lrolomeli/exoesqueleto-mano/programacion/pythongui/boton_stop.jpg

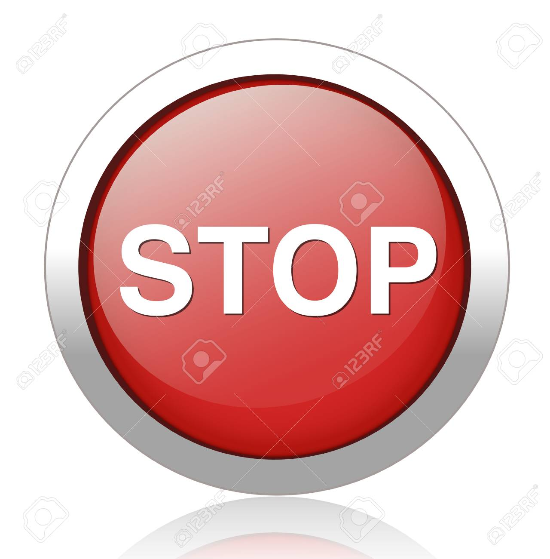
programacion/pythongui/boton_stop.jpg
