lrolomeli/exoesqueleto-mano/programacion/pythongui/boton_start.jpg

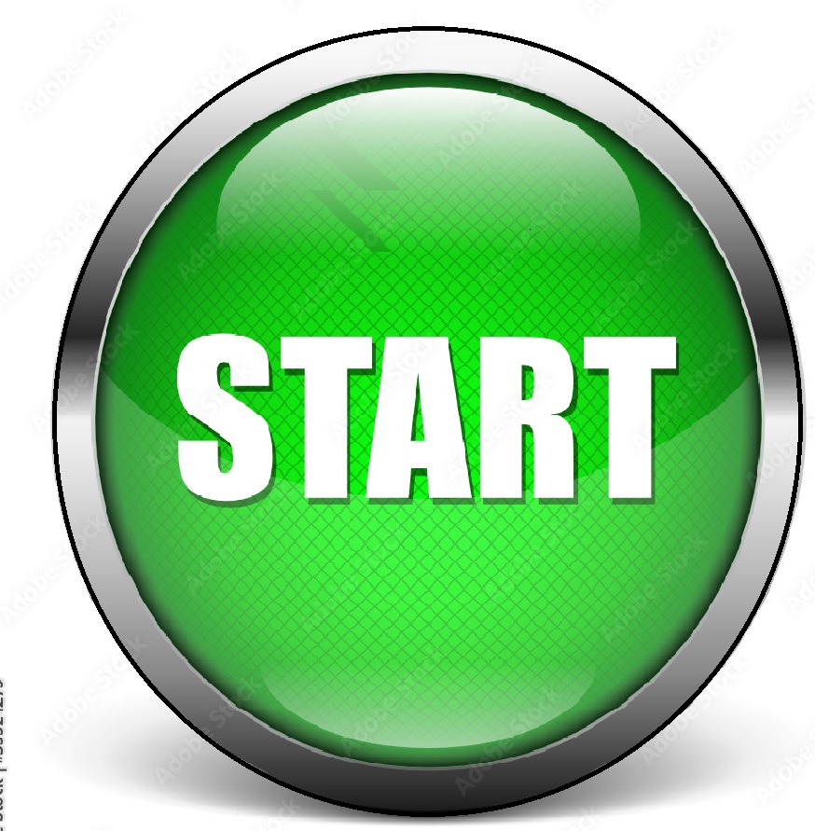
programacion/pythongui/boton_start.jpg
