lrolomeli/exoesqueleto-mano/programacion/pythongui/elegant.png

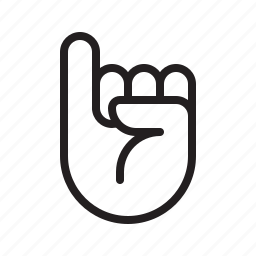
programacion/pythongui/elegant.png
