lrolomeli/exoesqueleto-mano/programacion/pythongui/exoesk.png

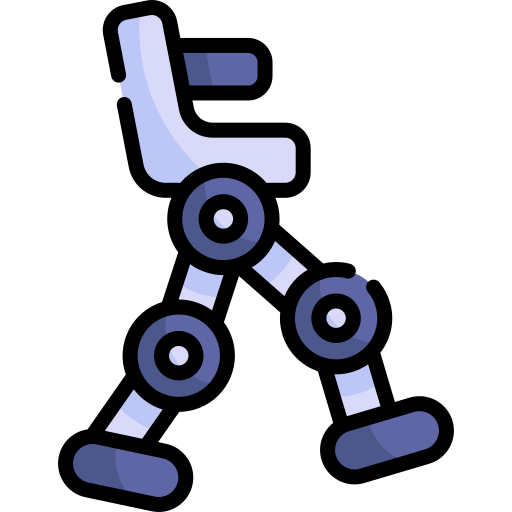
programacion/pythongui/exoesk.png
