lrolomeli/exoesqueleto-mano/programacion/pythongui/fdown.png

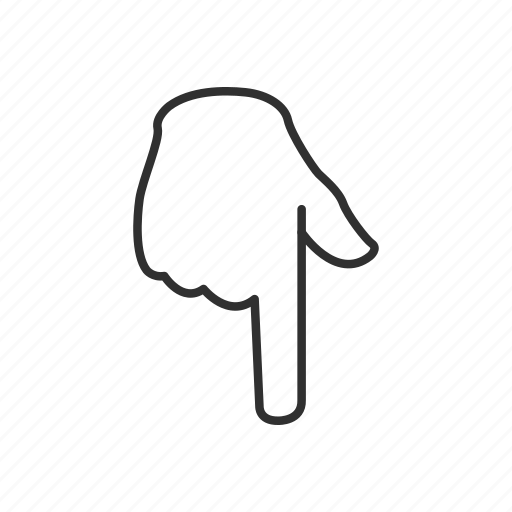
programacion/pythongui/fdown.png
