lrolomeli/exoesqueleto-mano/programacion/pythongui/left_hand.png

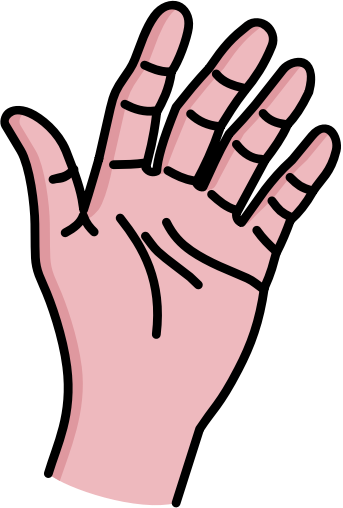
programacion/pythongui/left_hand.png
