lrolomeli/exoesqueleto-mano/programacion/pythongui/rck.png

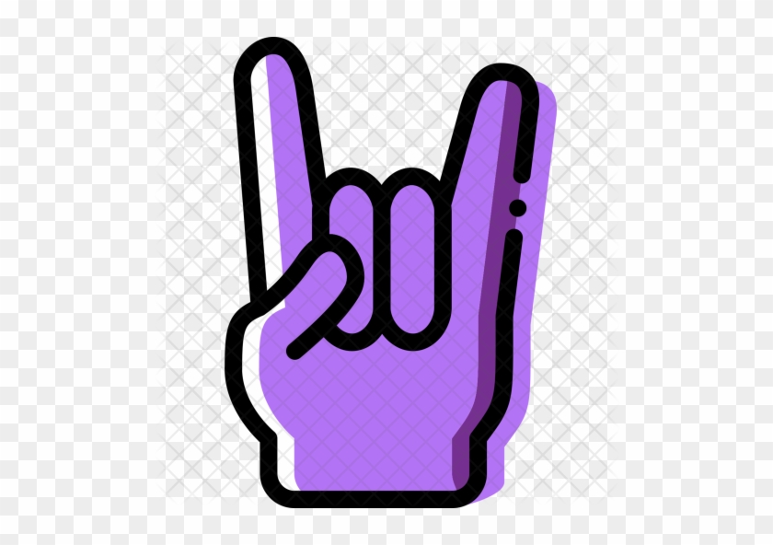
programacion/pythongui/rck.png
