lrolomeli/exoesqueleto-mano/programacion/pythongui/rocki.png

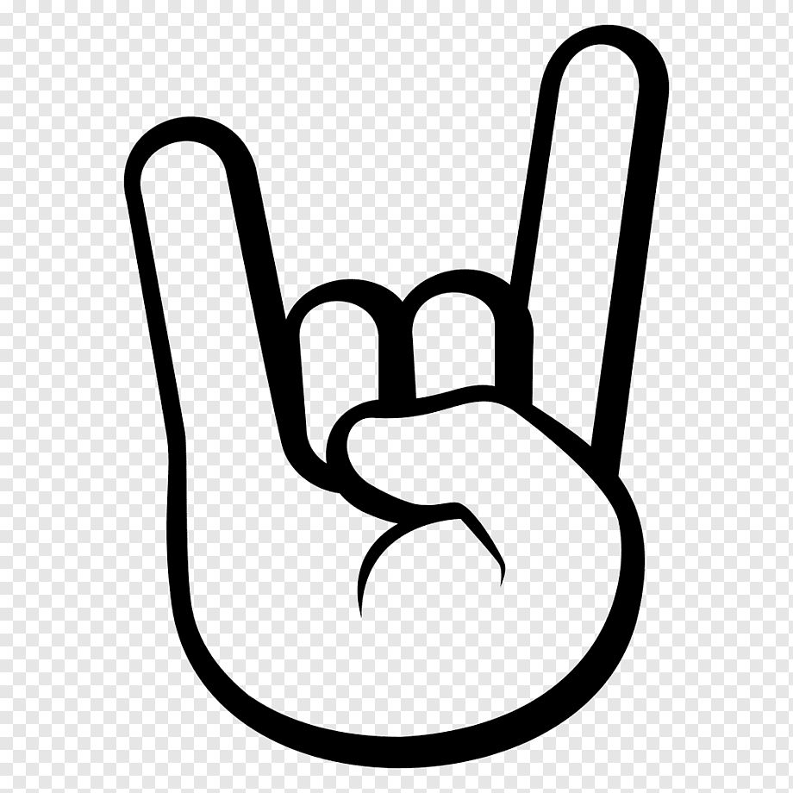
programacion/pythongui/rocki.png
