lrolomeli/exoesqueleto-mano/programacion/pythongui/start-button.jpg

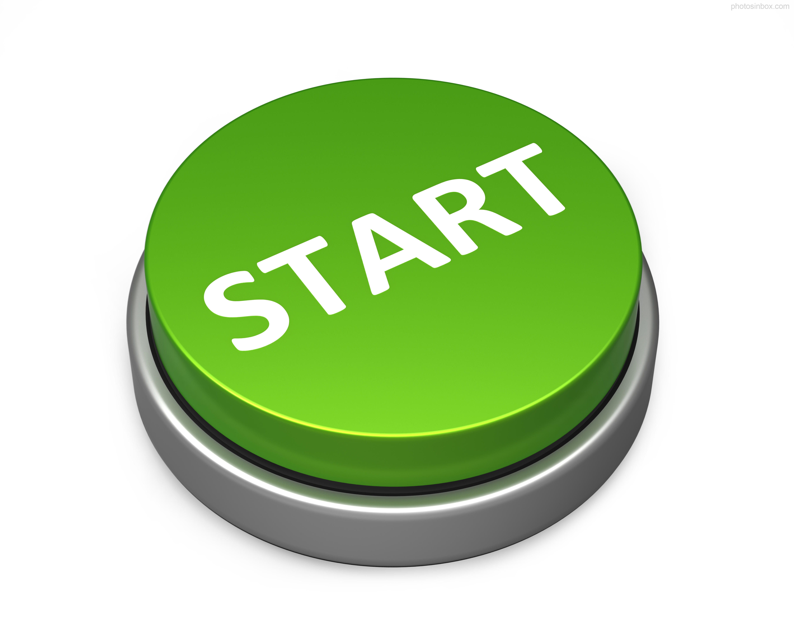
programacion/pythongui/start-button.jpg
