lrolomeli/exoesqueleto-mano/stl_impresion/cubierta1.STL

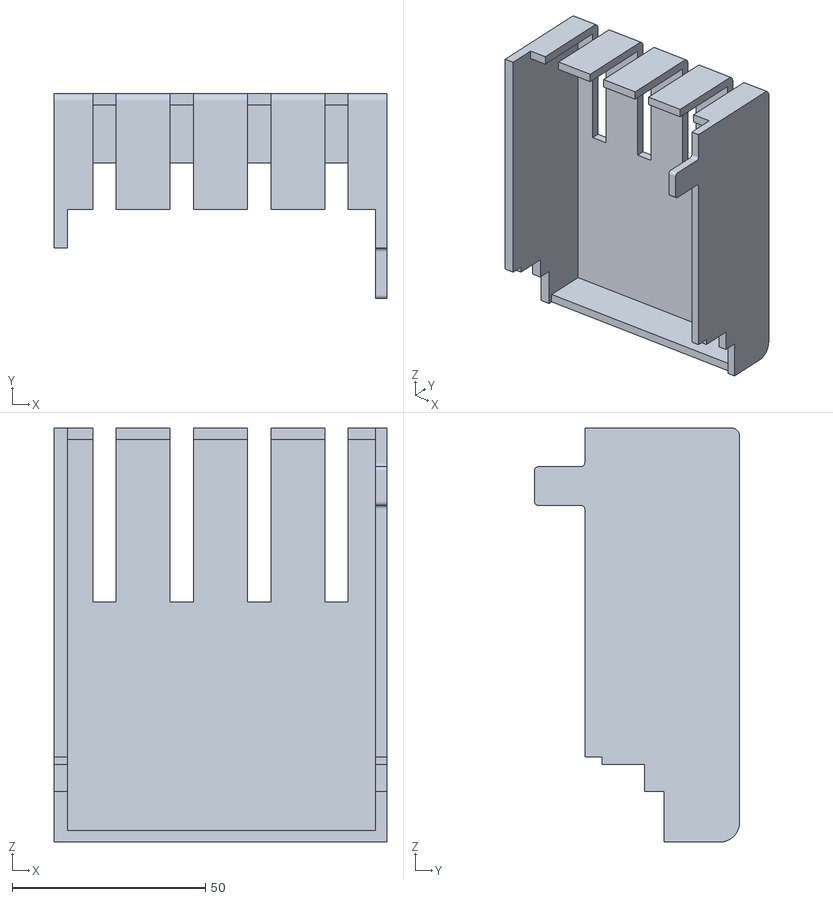
[picture p27: CAD file, 2023-11-08]
stl_impresion/cubierta1.STL
86.0 x 53.0 x 107.0
