lrolomeli/exoesqueleto-mano/mano_p/f3-medio.SLDPRT

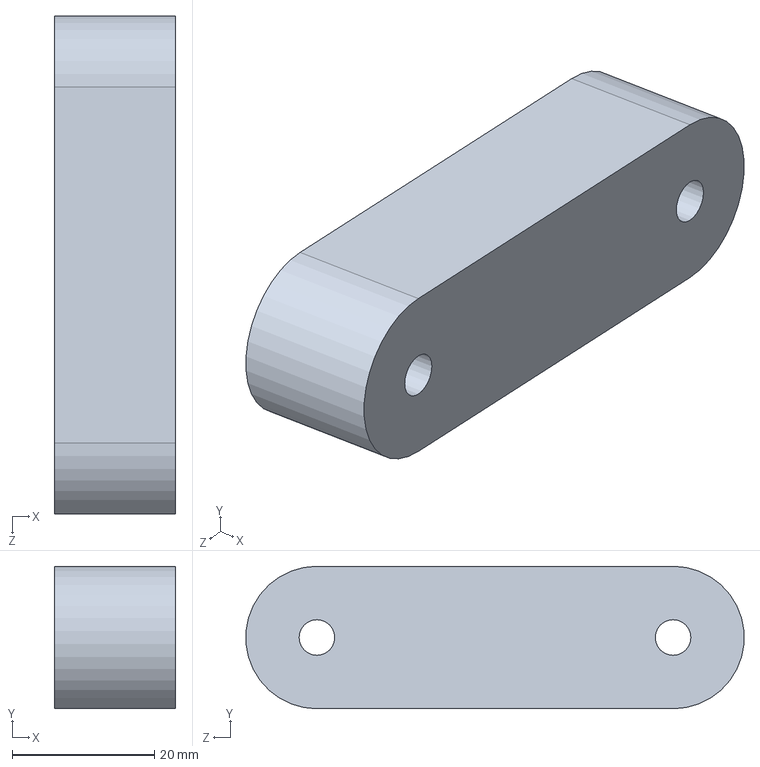
[picture p28: CAD file, 2023-06-01]
mano_p/f3-medio.SLDPRT
17.0 x 20.0 x 69.9 mm
