lrolomeli/exoesqueleto-mano/piezas/cubierta.SLDPRT

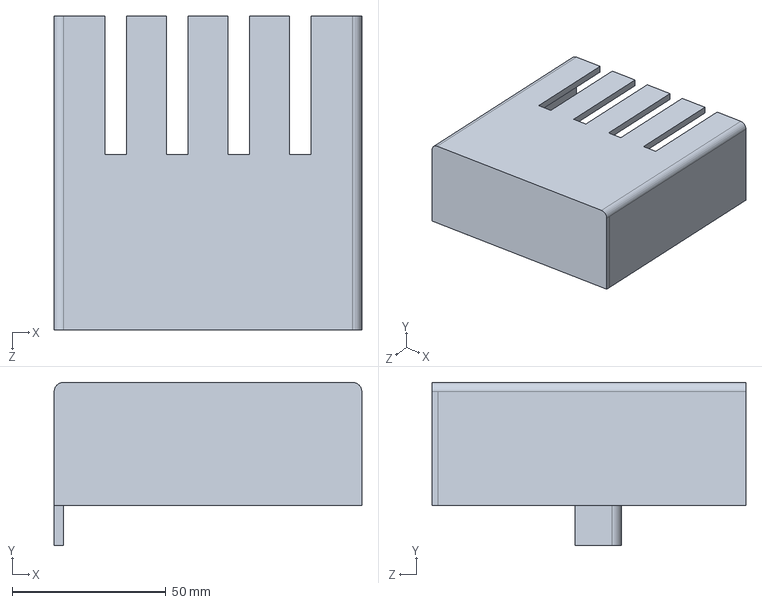
[picture p29: CAD file, 2023-11-08]
piezas/cubierta.SLDPRT
100.0 x 53.0 x 102.0 mm
