lrolomeli/exoesqueleto-mano/stl_impresion/vastago_pm.STL

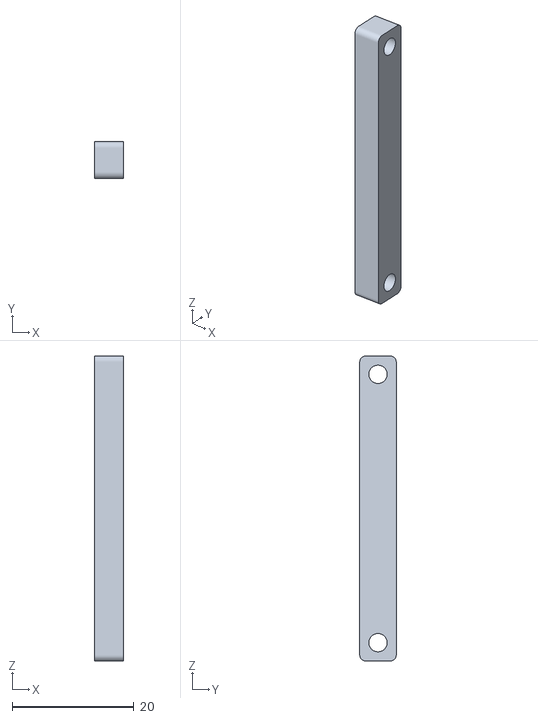
[picture p30: CAD file, 2023-09-11]
stl_impresion/vastago_pm.STL
4.80 x 6.00 x 50.0
