lrolomeli/exoesqueleto-mano/mano_p/f2-medio.SLDPRT

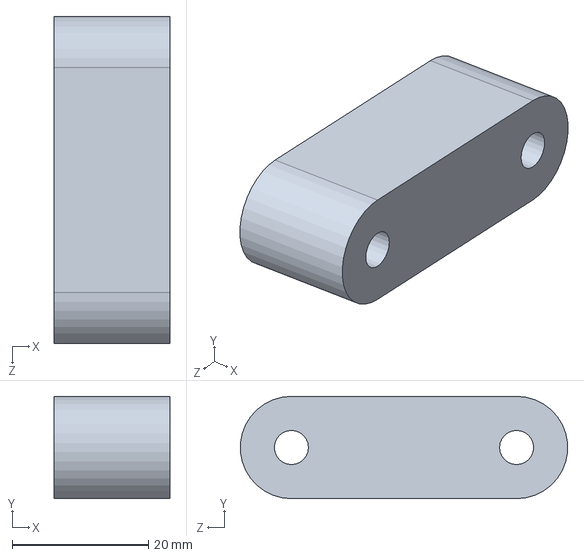
[picture p31: CAD file, 2023-06-01]
mano_p/f2-medio.SLDPRT
17.0 x 15.0 x 47.9 mm
