lrolomeli/exoesqueleto-mano/stl_impresion/tapa_base.STL

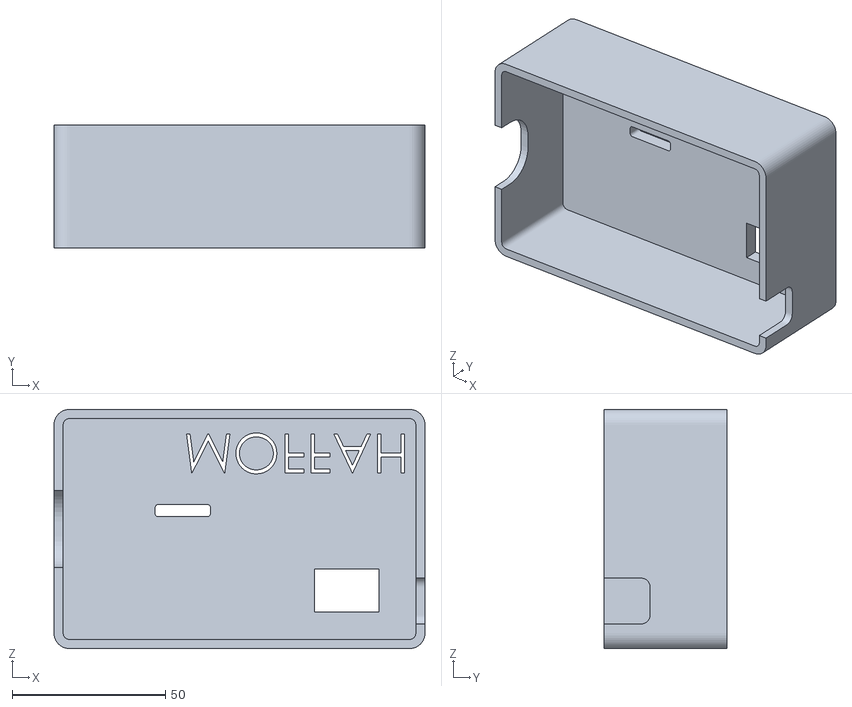
[picture p32: CAD file, 2023-09-11]
stl_impresion/tapa_base.STL
121.0 x 40.0 x 78.0
