lrolomeli/exoesqueleto-mano/mano_p/f1-medio.SLDPRT

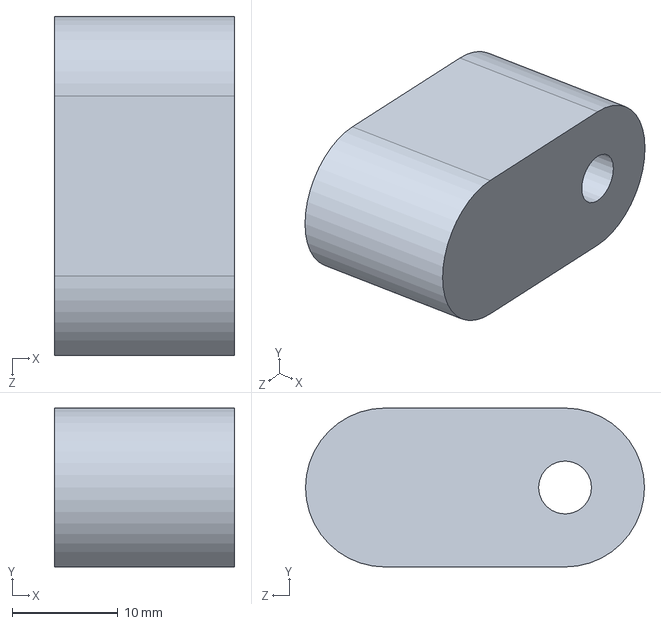
[picture p33: CAD file, 2023-06-01]
mano_p/f1-medio.SLDPRT
17.0 x 15.0 x 32.0 mm
