lrolomeli/exoesqueleto-mano/stl_impresion/base_bateria_pcb.STL

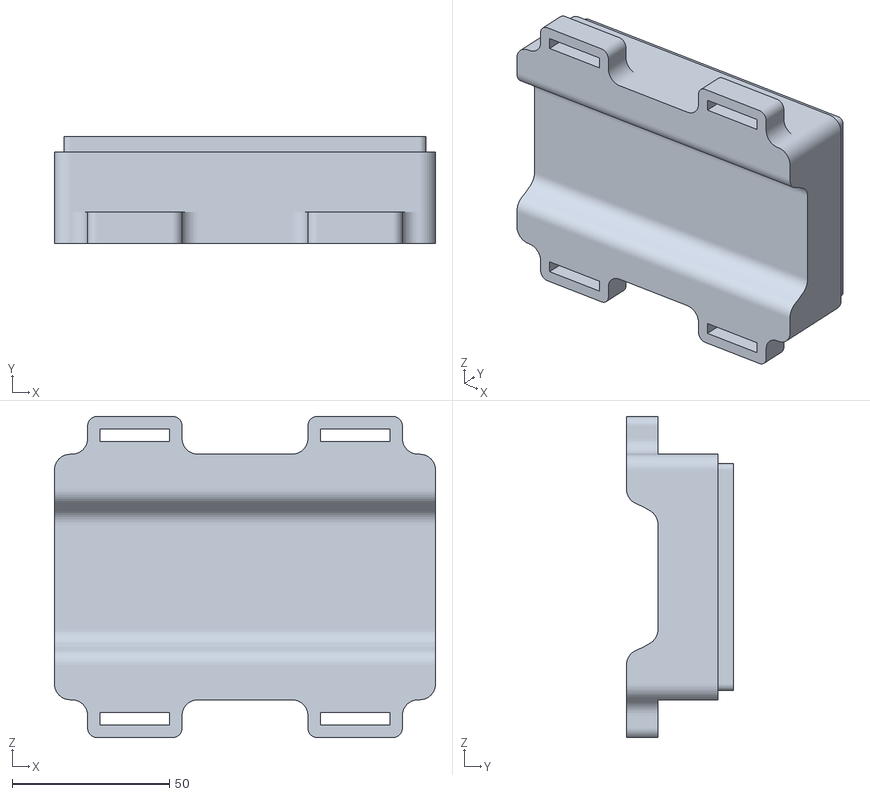
[picture p34: CAD file, 2023-09-11]
stl_impresion/base_bateria_pcb.STL
121.0 x 34.0 x 102.0
