lrolomeli/exoesqueleto-mano/stl_impresion/vastago-y-largo-pulgar.STL

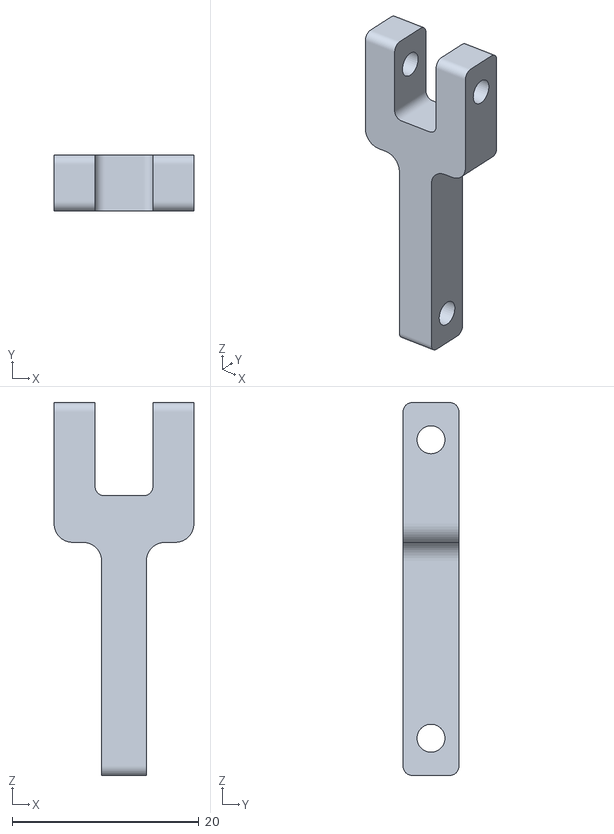
[picture p35: CAD file, 2023-09-11]
stl_impresion/vastago-y-largo-pulgar.STL
15.0 x 6.00 x 40.0
