lrolomeli/exoesqueleto-mano/mano_p/f3-anular.SLDPRT

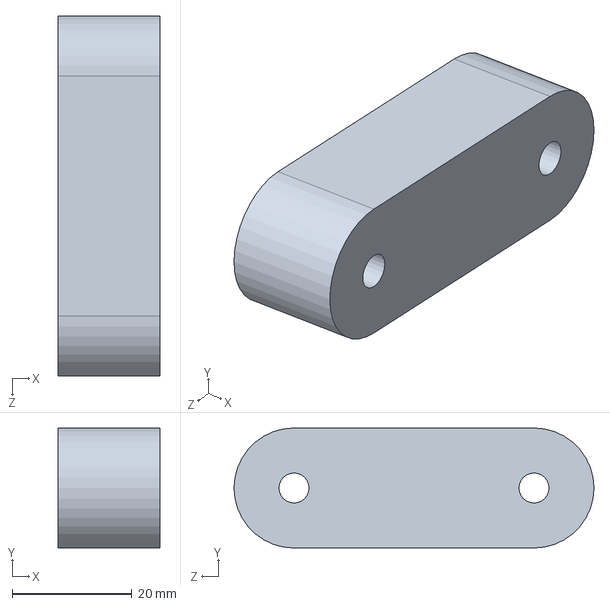
[picture p36: CAD file, 2023-06-01]
mano_p/f3-anular.SLDPRT
17.0 x 20.0 x 60.0 mm
