lrolomeli/exoesqueleto-mano/mano_p/torso-mano.SLDPRT

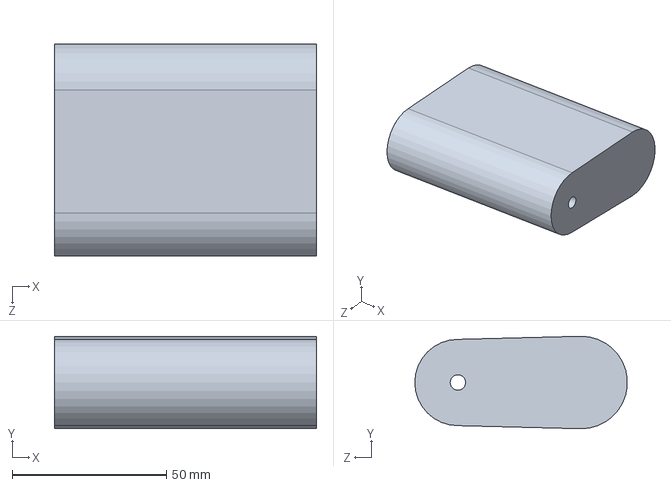
[picture p37: CAD file, 2023-05-29]
mano_p/torso-mano.SLDPRT
85.0 x 30.0 x 68.9 mm
