lrolomeli/exoesqueleto-mano/piezas/vastago-y-largo-indice.SLDPRT

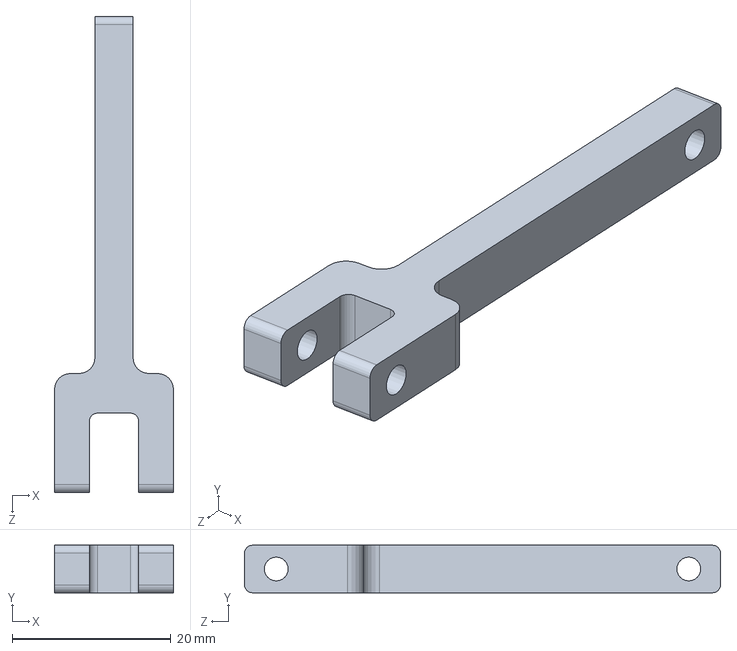
[picture p38: CAD file, 2023-09-11]
piezas/vastago-y-largo-indice.SLDPRT
15.0 x 6.00 x 60.0 mm
