lrolomeli/exoesqueleto-mano/stl_impresion/abrazadera_completa.STL

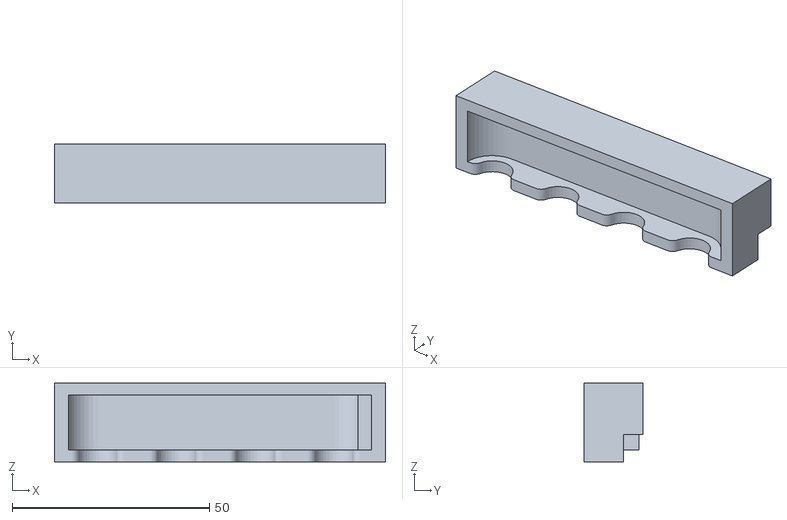
[picture p39: CAD file, 2023-07-09]
stl_impresion/abrazadera_completa.STL
84.0 x 15.0 x 20.0
