lrolomeli/exoesqueleto-mano/stl_impresion/abrazadera_completa_2pza.STL

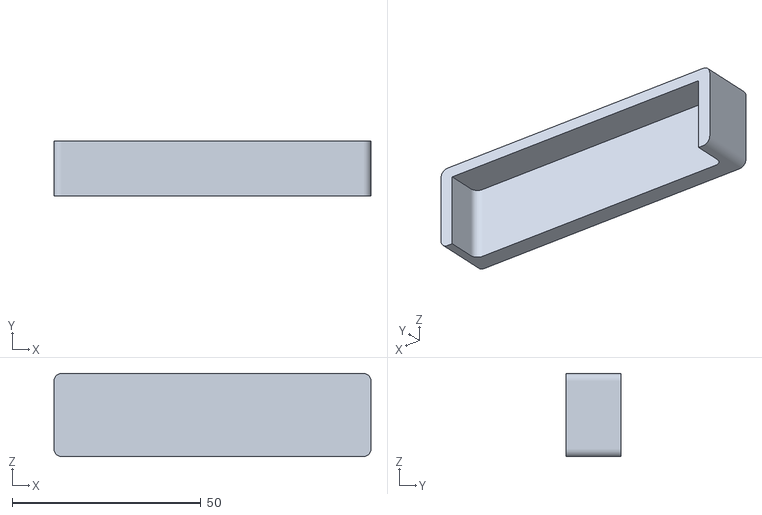
[picture p40: CAD file, 2023-07-09]
stl_impresion/abrazadera_completa_2pza.STL
84.0 x 14.5 x 22.0
