lrolomeli/exoesqueleto-mano/piezas/cincho_belcro.SLDPRT

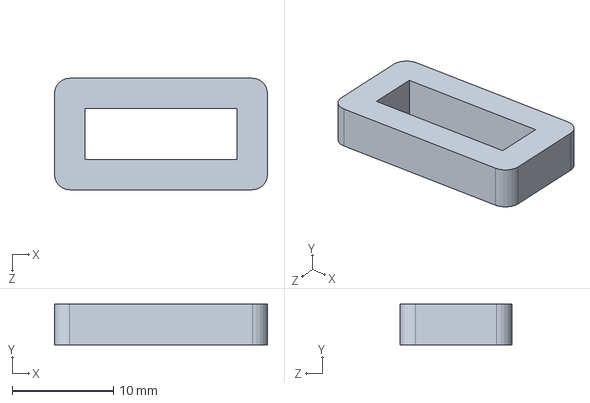
[picture p41: CAD file, 2023-07-09]
piezas/cincho_belcro.SLDPRT
21.0 x 4.00 x 11.0 mm
