lrolomeli/exoesqueleto-mano/stl_impresion/palanca-medio.STL

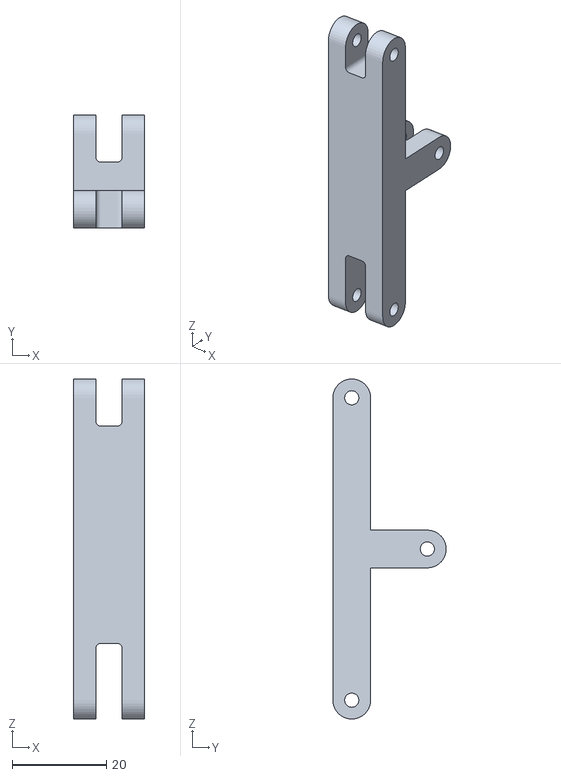
[picture p42: CAD file, 2023-07-03]
stl_impresion/palanca-medio.STL
15.0 x 24.0 x 72.0
