lrolomeli/exoesqueleto-mano/mano_p/f2-anular.SLDPRT

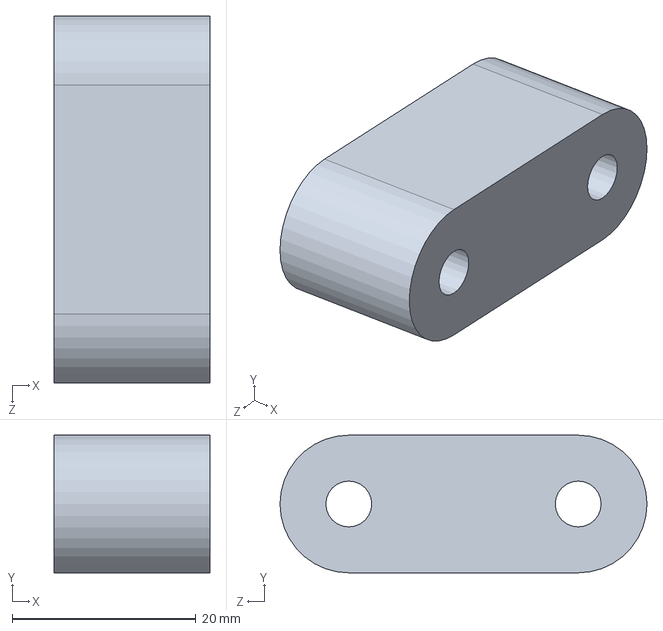
[picture p43: CAD file, 2023-05-08]
mano_p/f2-anular.SLDPRT
17.0 x 15.0 x 40.0 mm
