lrolomeli/exoesqueleto-mano/stl_impresion/base-principal-p2.STL

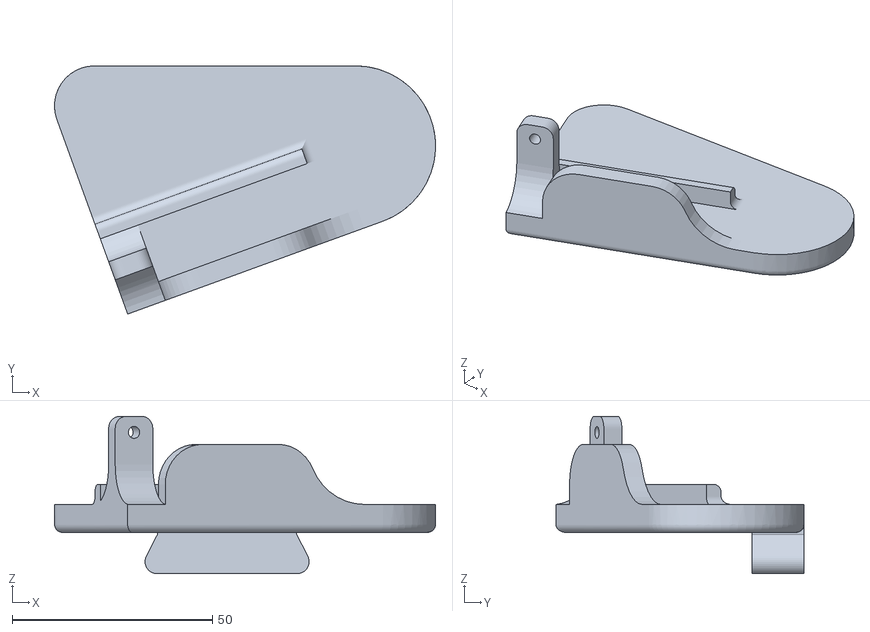
[picture p44: CAD file, 2023-07-03]
stl_impresion/base-principal-p2.STL
95.2 x 62.0 x 39.3
