lrolomeli/exoesqueleto-mano/mano_p/falange4_p.SLDPRT

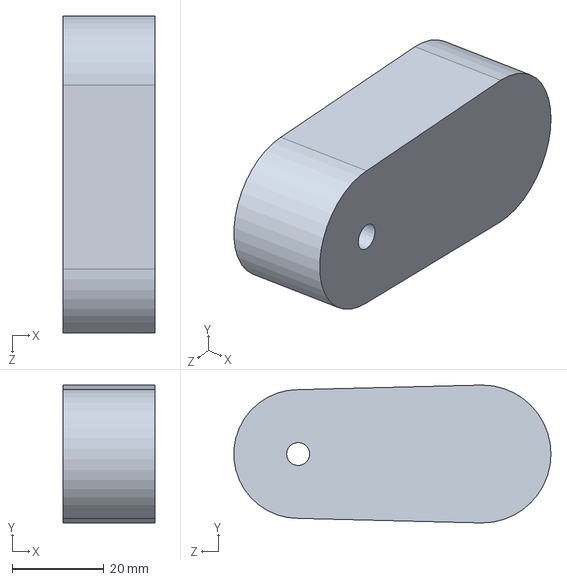
[picture p45: CAD file, 2023-05-08]
mano_p/falange4_p.SLDPRT
20.0 x 30.0 x 69.0 mm
