lrolomeli/exoesqueleto-mano/stl_impresion/base-principal-completa.STL

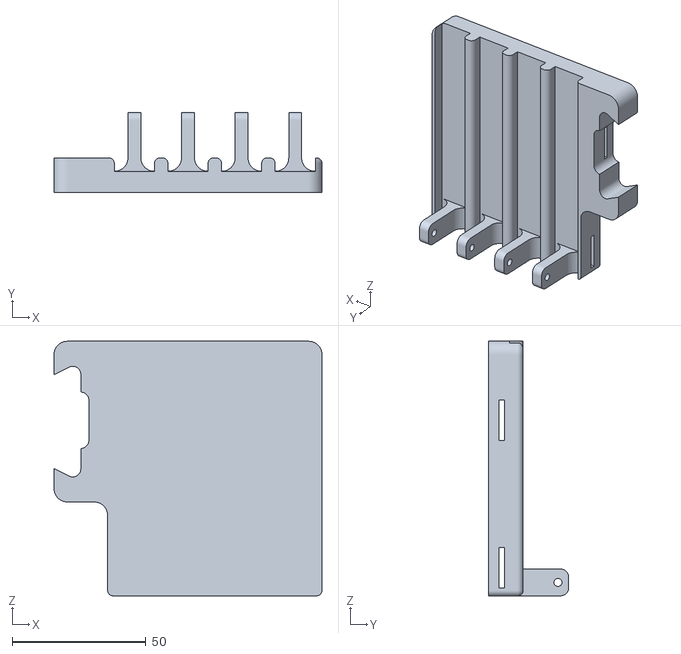
[picture p46: CAD file, 2023-07-03]
stl_impresion/base-principal-completa.STL
100.0 x 30.0 x 95.0
