lrolomeli/exoesqueleto-mano/piezas/abrazadera.SLDPRT

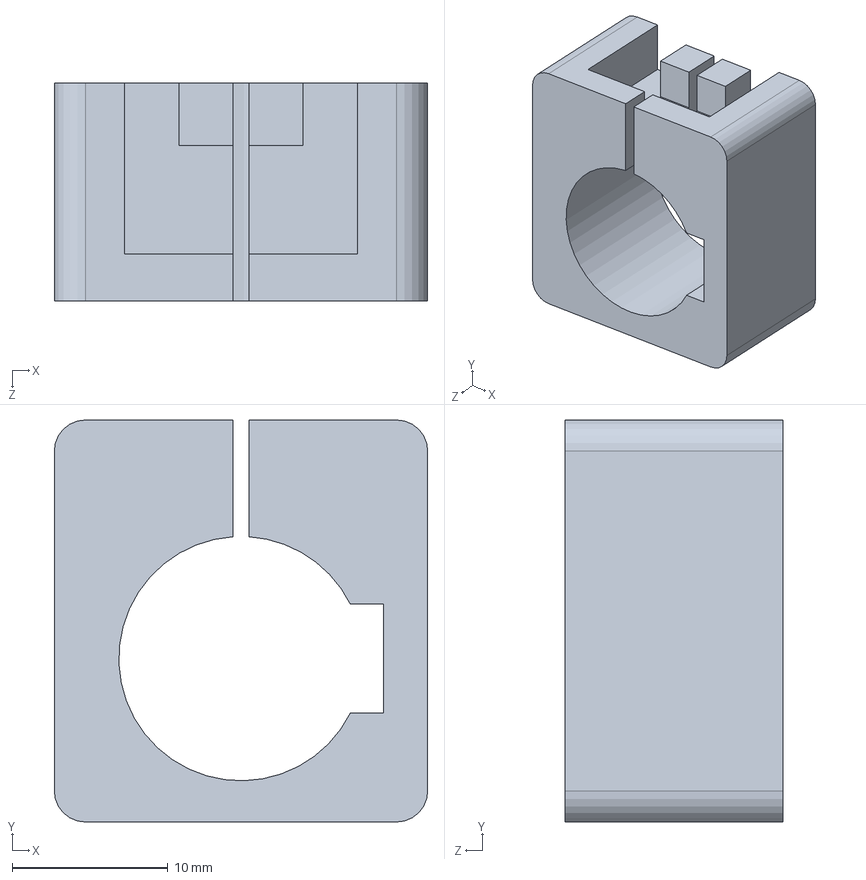
[picture p47: CAD file, 2023-07-03]
piezas/abrazadera.SLDPRT
24.0 x 25.8 x 14.0 mm
