lrolomeli/exoesqueleto-mano/piezas/guia-lineal.SLDPRT

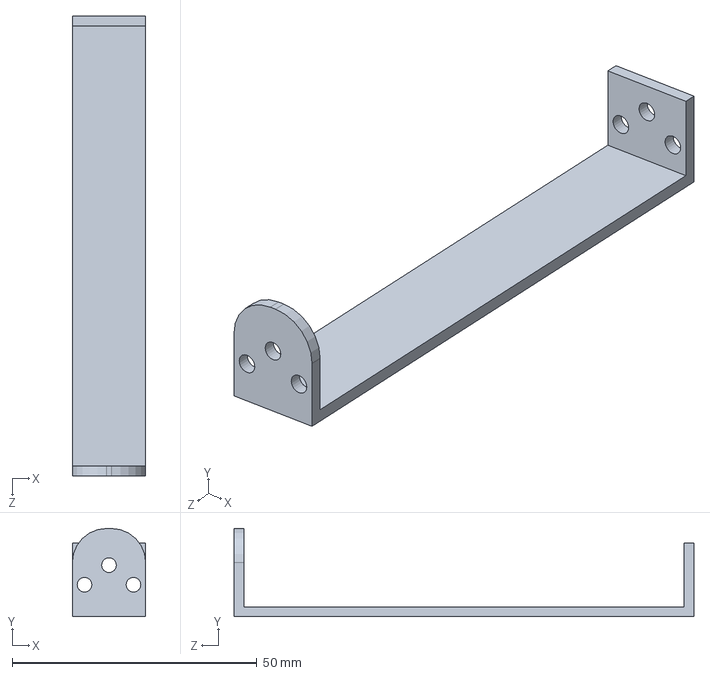
[picture p48: CAD file, 2023-07-03]
piezas/guia-lineal.SLDPRT
15.0 x 18.0 x 94.0 mm
