lrolomeli/exoesqueleto-mano/stl_impresion/vastago-y-largo-menique.STL

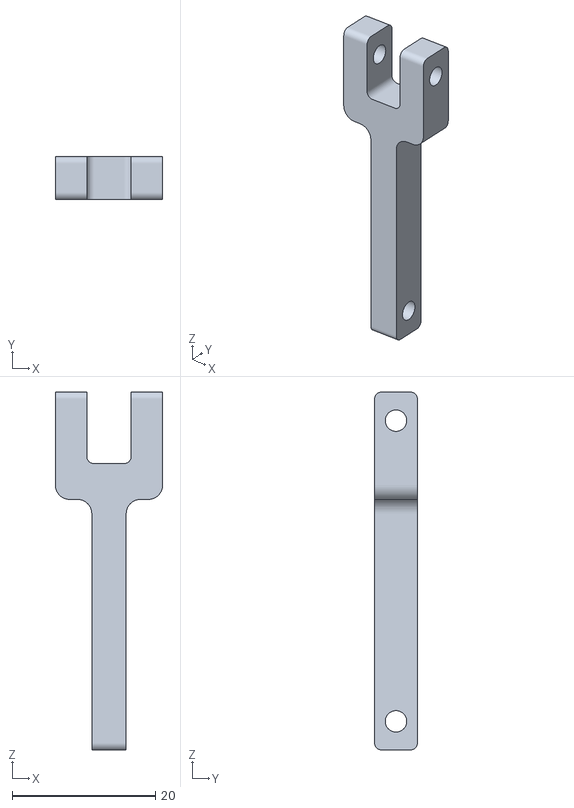
[picture p49: CAD file, 2023-07-03]
stl_impresion/vastago-y-largo-menique.STL
15.0 x 6.00 x 50.0
