lrolomeli/exoesqueleto-mano/piezas/palanca-medio.SLDPRT

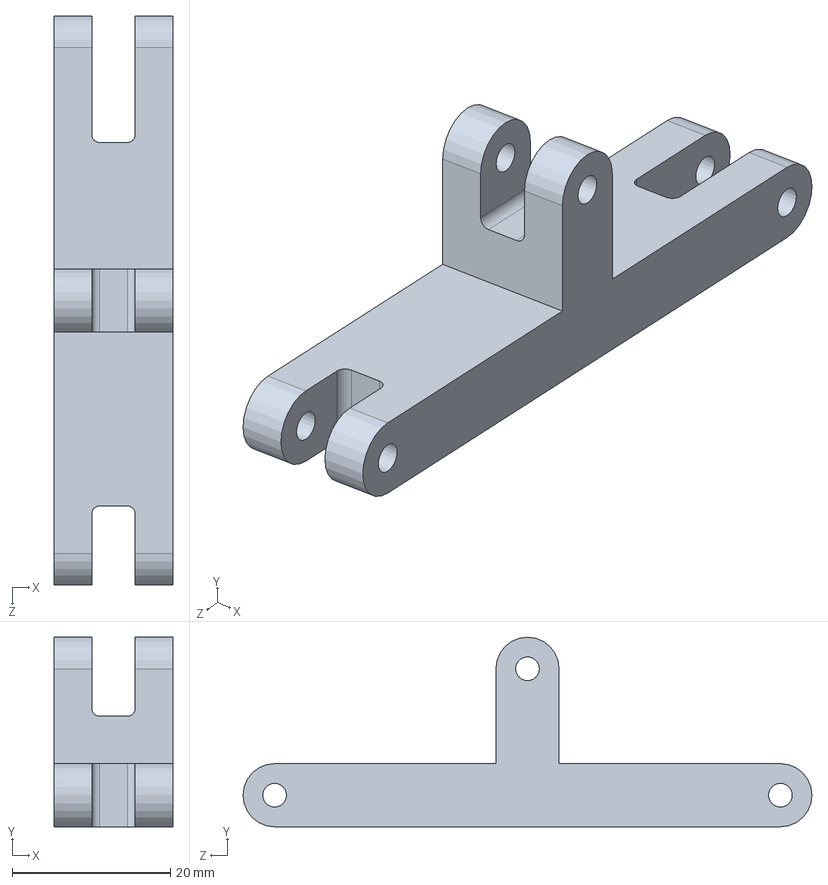
[picture p50: CAD file, 2023-07-02]
piezas/palanca-medio.SLDPRT
15.0 x 24.0 x 72.0 mm
