lrolomeli/exoesqueleto-mano/stl_impresion/entronque_barra_ref.STL

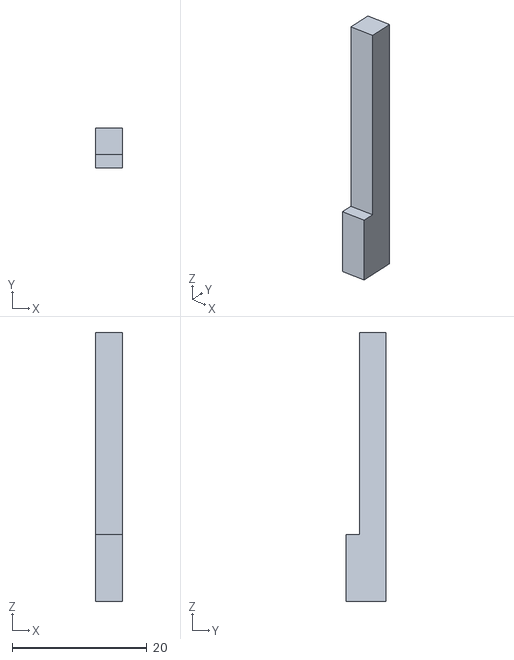
[picture p51: CAD file, 2023-07-02]
stl_impresion/entronque_barra_ref.STL
4.00 x 6.00 x 40.0
