lrolomeli/exoesqueleto-mano/stl_impresion/vastago.STL

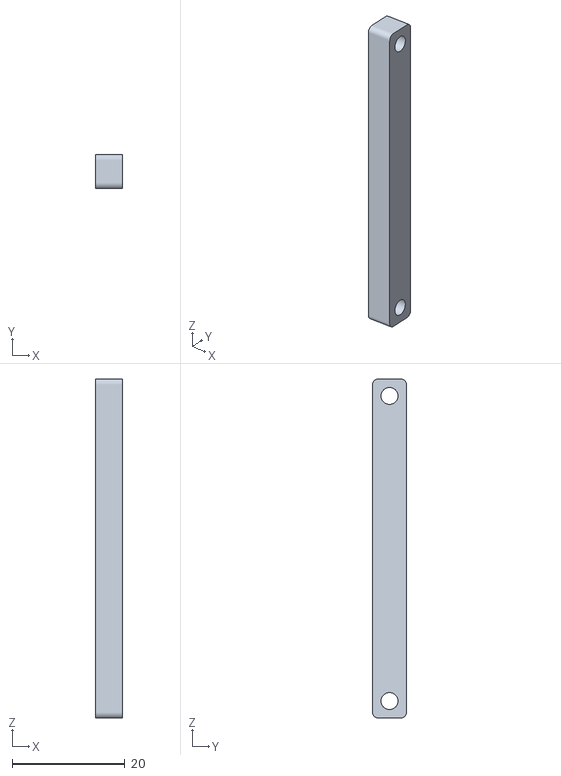
[picture p52: CAD file, 2023-07-02]
stl_impresion/vastago.STL
4.80 x 6.00 x 60.0
