lrolomeli/exoesqueleto-mano/piezas/vastago-y-largo-medio.SLDPRT

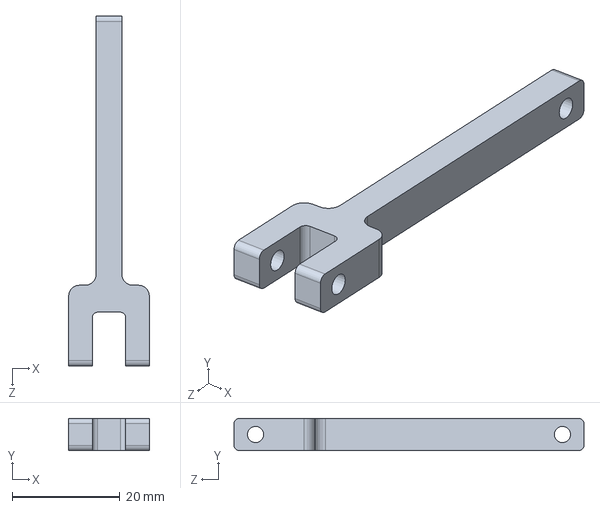
[picture p53: CAD file, 2023-07-02]
piezas/vastago-y-largo-medio.SLDPRT
15.0 x 6.00 x 65.0 mm
