lrolomeli/exoesqueleto-mano/stl_impresion/falangefinal.STL

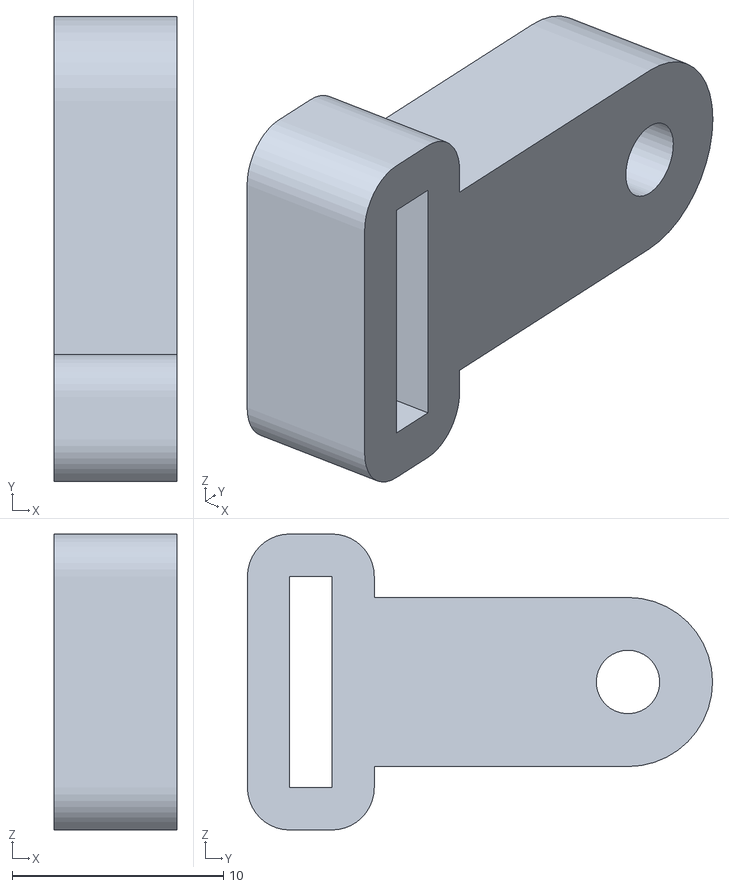
[picture p54: CAD file, 2023-05-29]
stl_impresion/falangefinal.STL
5.80 x 22.0 x 14.0
