lrolomeli/exoesqueleto-mano/piezas/palanca-anular.SLDPRT

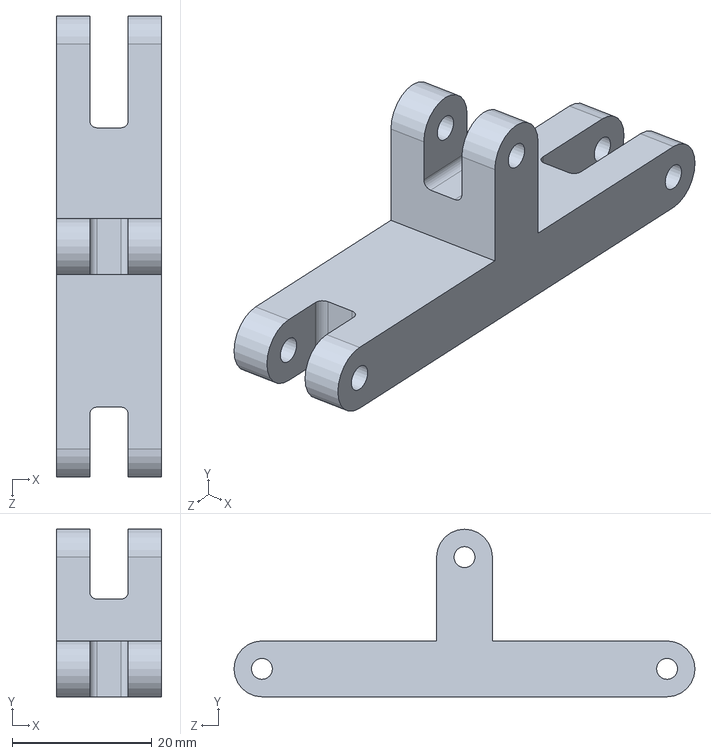
[picture p55: CAD file, 2023-07-02]
piezas/palanca-anular.SLDPRT
15.0 x 24.0 x 66.0 mm
