lrolomeli/exoesqueleto-mano/piezas/union-motor_original.SLDPRT

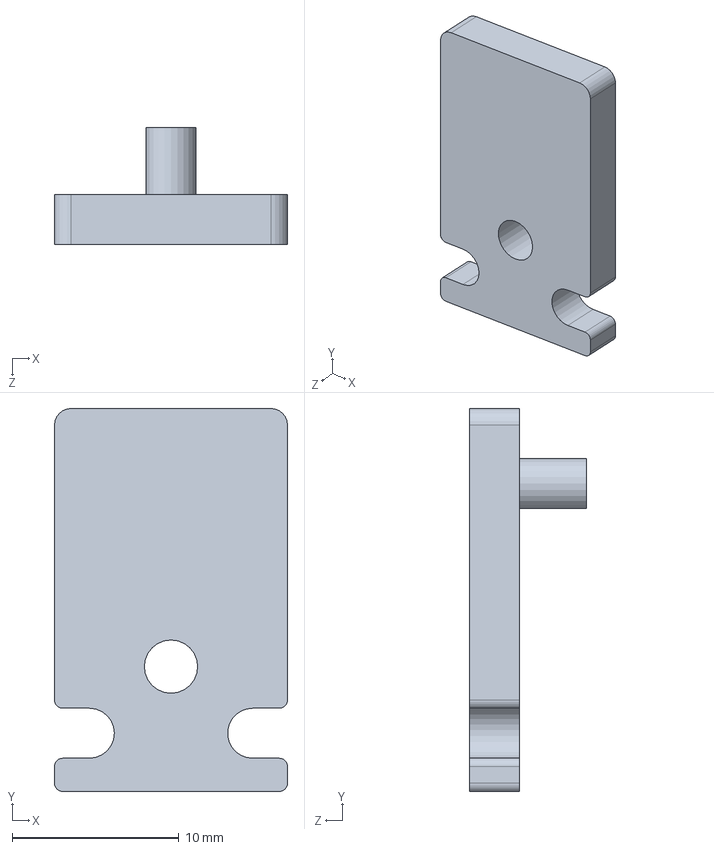
[picture p56: CAD file, 2023-06-30]
piezas/union-motor_original.SLDPRT
14.0 x 23.0 x 7.00 mm
