lrolomeli/exoesqueleto-mano/piezas/tornillo.SLDPRT

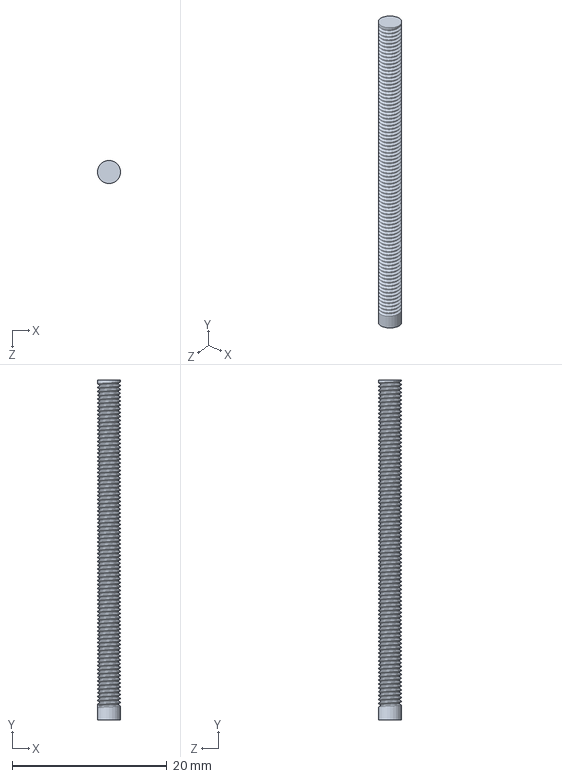
[picture p57: CAD file, 2023-06-01]
piezas/tornillo.SLDPRT
3.00 x 44.0 x 3.00 mm
