lrolomeli/exoesqueleto-mano/piezas/motor15mm.SLDPRT

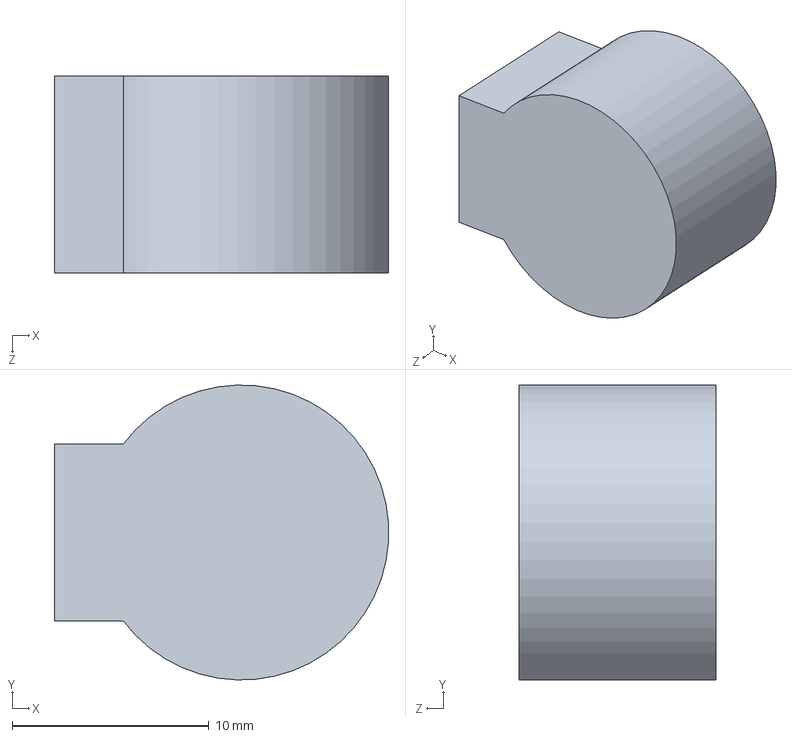
[picture p58: CAD file, 2023-06-01]
piezas/motor15mm.SLDPRT
17.0 x 15.0 x 10.0 mm
