lrolomeli/exoesqueleto-mano/piezas/perno-lineal.SLDPRT

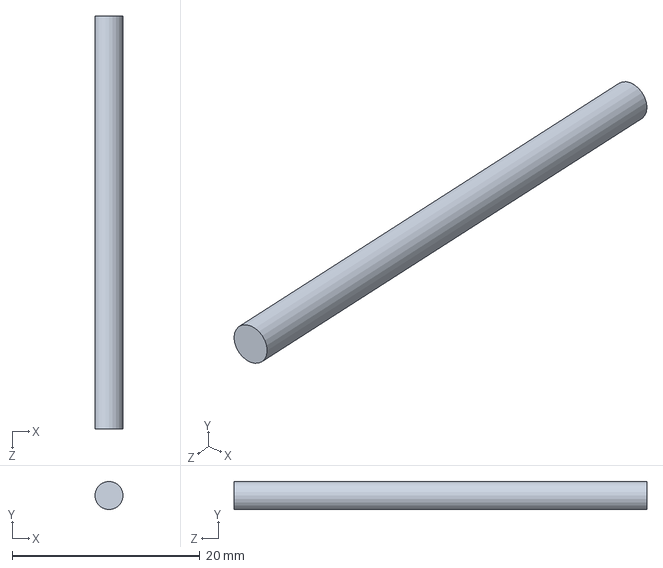
[picture p59: CAD file, 2023-06-01]
piezas/perno-lineal.SLDPRT
3.00 x 3.00 x 44.0 mm
